pinto0528/alpa/Documentacion/Modelo_de_negocio/canales_relacion.md

# Canales y Relación con Clientes

## Canales de Distribución

El sistema se distribuye a través de tres canales principales, segmentados según el tipo de cliente:

| Canal | Segmento | Descripción |
|---|---|---|
| **Venta directa** | Productores agropecuarios | El equipo comercial contacta directamente al productor, realiza una visita al campo para relevar necesidades, propone una configuración de nodos y gateway, y gestiona la instalación. |
| **Alianzas con aseguradoras** | Aseguradoras agrícolas (B2B) | Las aseguradoras incluyen el sistema como beneficio o requisito en sus pólizas. La venta se canaliza a través de la aseguradora, que actúa como prescriptora y canal de distribución masivo. |
| **Cooperativas y asociaciones agrícolas** | Productores asociados | Las cooperativas difunden el sistema entre sus miembros, facilitan la compra grupal (descuentos por volumen) y centralizan la instalación en una zona geográfica, reduciendo costos logísticos. |

### Esquema de Distribución por Segmento

| Segmento | Canal Primario | Canal Secundario | Modelo de Venta |
|---|---|---|---|
| **Productor pequeño-mediano** | Cooperativa / asociación | Venta directa digital | Kit básico, pago financiado |
| **Productor mediano-grande** | Venta directa | Aseguradora (derivación) | Kit estándar, contado o suscripción anual |
| **Agroindustria / ingenio** | Venta directa corporativa | Aseguradora (co-branding) | Kit premium, suscripción corporativa |
| **Aseguradora** | Comercial B2B | — | Licencia anual por cliente asegurado |
| **Gobierno / municipio** | Licitación / convenio | — | Licencia institucional por territorio |

---

## Canales de Comunicación

| Canal | Propósito | Segmento |
|---|---|---|
| **Sitio web institucional** | Presentación del sistema, casos de uso, solicitud de contacto, tienda online | Todos los segmentos |
| **Demostraciones en campo** | Instalación piloto gratuita en campos de productores referentes. Validación en terreno con bomberos. | Productores, bomberos, HyS |
| **Referencias de productores** | Programa de embajadores: productores que ya usan el sistema recomiendan a pares. Efecto "boca a boca" en zonas rurales. | Productores |
| **Redes comerciales de aseguradoras** | Los ejecutivos de cuenta de las aseguradoras ofrecen el sistema a sus asegurados como servicio de prevención. | Productores (vía aseguradora) |
| **Charlas y capacitaciones** | Talleres en cooperativas, sociedades rurales y facultades. Demostración del impacto del sistema. | Productores, bomberos, estudiantes |
| **Atención telefónica / WhatsApp** | Soporte pre-venta y post-venta. Canal directo con el equipo emprendedor. | Todos los segmentos |

---

## Relación con Productores

### Antes de la Venta (Captación)

1. **Contacto inicial:** el productor llega por referencia, web, aseguradora o cooperativa
2. **Relevamiento del campo:** visita técnica para evaluar extensión, topografía, puntos críticos, conectividad disponible
3. **Propuesta personalizada:** configuración de nodos y gateway según las necesidades del establecimiento
4. **Demostración:** instalación de 1-2 nodos de prueba por 15 días para que el productor valide el funcionamiento

### Durante la Venta (Instalación)

| Actividad | Responsable | Duración Estimada |
|---|---|---|
| Instalación de nodos en campo | Técnico de campo | 1 día para predios de hasta 500 ha |
| Configuración de gateway y conectividad | Técnico de campo | 2-3 horas |
| Capacitación del productor y su personal | Técnico de campo | 2 horas |
| Activación de dashboard y alertas | Equipo de software | Inmediato |

### Post-Venta

| Actividad | Frecuencia | Canal |
|---|---|---|
| **Soporte técnico** | 24/7 para emergencias, horario laboral para consultas generales | WhatsApp / llamada / remoto |
| **Actualización de firmware** | Trimestral o ante nueva funcionalidad | OTA (over-the-air) vía gateway |
| **Mantenimiento preventivo** | Semestral (antes de temporada crítica) | Visita técnica |
| **Reporte de actividad** | Mensual vía email | Dashboard exportable |
| **Renovación de suscripción** | Anual | Automática / recordatorio |

---

## Relación con Aseguradoras

| Actividad | Frecuencia | Descripción |
|---|---|---|
| **Reportes periódicos de siniestralidad** | Trimestral | Dashboard con métricas de los asegurados que tienen el sistema instalado: alertas disparadas, tiempo de respuesta, siniestros evitados. |
| **Auditoría de datos** | Anual | Verificación independiente de la integridad de los registros del sistema. Cada evento tiene un hash que garantiza su inalterabilidad. |
| **Reuniones comerciales** | Bimestral | Revisión de métricas de adopción, ajuste de bonificaciones, planificación de nuevos despliegues. |
| **Co-branding** | Por campaña | Material de comunicación conjunto: la aseguradora comunica el beneficio a sus asegurados con la marca del sistema. |

### Modelo de Relación

> La aseguradora no es solo un cliente: es un **canal de distribución estratégico**. Su fuerza de ventas ya tiene relación con los productores. Cada ejecutivo de cuenta que recomienda el sistema es un vendedor en terreno sin costo fijo para el proyecto.

---

## Captación de Clientes por Etapa

| Etapa | Actividad | Métrica de Éxito |
|---|---|---|
| **Lanzamiento (Año 1)** | Demostraciones gratuitas en 10 campos de productores referentes en Tucumán. Charlas en 3 cooperativas agrícolas. Presentación en 2 ingenios azucareros. | 10 instalaciones piloto, 35 kits vendidos |
| **Crecimiento (Año 2)** | Programa de referidos con descuento. Alianza con 1 aseguradora. Presencia en 2 ferias agrícolas del NOA. | 85 kits vendidos, 30% por canal aseguradora |
| **Expansión (Año 3)** | Expansión a Córdoba y Litoral. 2 aseguradoras activas. Distribución en cooperativas de 4 provincias. | 190 kits vendidos, 50% por canal aseguradora |

---

## Matriz de Canales y Relación por Segmento

| Segmento | Canal de Distribución | Canal de Comunicación | Tipo de Relación | Intensidad |
|---|---|---|---|---|
| **Productor** | Venta directa / cooperativa / aseguradora | WhatsApp, demostraciones, referidos | Personalizada, soporte técnico continuo | Alta |
| **Aseguradora** | Comercial B2B | Reportes, reuniones, dashboard | Contractual, datos auditables | Alta |
| **Bomberos / brigadas** | Sin costo (beneficiario estratégico) | Coordinación directa | Colaboración, validación técnica | Media |
| **HyS industrial** | Venta directa corporativa | Demostraciones, capacitaciones | Técnica, cumplimiento normativo | Media |
| **Gobierno / municipio** | Licitación / convenio | Presentaciones institucionales | Contractual, monitoreo territorial | Baja (escalamiento futuro) |

---

*Documento perteneciente al proyecto Sistema de Alerta de Incendios Rurales*
