pinto0528/alpa/Documentacion/Modelo_de_negocio/propuesta_valor.md

# Propuesta de Valor

## Declaración de Propuesta de Valor

Un sistema autónomo de detección temprana de incendios que alerta al productor agropecuario en menos de 5 minutos —sin depender de señal celular, electricidad de red ni vigilancia humana— evitando pérdidas millonarias, protegiendo vidas y reduciendo el tiempo de respuesta de 40 minutos a minutos.

---

## Mapa de Valor por Segmento

### 1. Para Productores Agropecuarios

#### Beneficios

| Beneficio | Descripción | Impacto Cuantitativo |
|---|---|---|
| **Detección en menos de 5 minutos** | Sensores detectan humo, temperatura anormal o llama en etapa incipiente y disparan alerta inmediata | Reduce tiempo de detección de 30-40 min a <5 min |
| **Sin dependencia de conectividad** | Comunicación vía LoRa/LoRaWAN entre nodos y gateway. No requiere señal celular ni internet | Opera en el 100% del campo, incluso en zonas sin cobertura |
| **Autonomía energética total** | Paneles solares + baterías. No requiere conexión a red eléctrica | Funcionamiento continuo 24/7 durante toda la temporada crítica |
| **Alerta con geolocalización GPS** | Cada alerta incluye coordenadas exactas del nodo que detectó el evento | Permite ir directo al foco sin perder tiempo buscando |
| **Cobertura 24/7** | Monitoreo continuo, incluso de noche o en zonas alejadas | Donde hoy es imposible tener ojos, el sistema nunca se desconecta |
| **Reportes digitales para seguros** | Registro inalterable de activación, alertas y estado del sistema | Respaldos para reclamar bonificaciones de póliza o agilizar indemnizaciones |
| **Protección de activos críticos** | Cobertura específica para zonas de alto valor: sistemas de riego, galpones, cultivos intensivos | Un incendio detectado a tiempo puede salvar USD 80.000+ en infraestructura de riego |

#### Aliviadores de Dolores Específicos

| Dolor Actual | Cómo lo Alivia el Sistema |
|---|---|
| *"Nos enteramos siempre tarde"* | Alerta automática en <5 minutos desde que se inicia el foco |
| *"De noche es imposible tener ojos en todos lados"* | Sensores infrarrojos + detección de humo funcionan 24/7 |
| *"La señal de celular ahí adentro es nula"* | Comunicación LoRa sin necesidad de antena celular ni internet |
| *"Perdí 40 ha de limón y USD 80.000 en riego"* | Detección temprana permite actuar antes de que el fuego alcance zonas críticas |
| *"Te da una impotencia bárbara no poder hacer nada"* | Pasividad → Proactividad. El productor recibe la alerta y actúa en minutos |

#### Propuesta de Valor en una Frase

> "Sepa dónde y cuándo se inició un incendio en su campo, aunque no haya señal celular, antes de que sea demasiado tarde."

---

### 2. Para Aseguradoras Agrícolas

#### Beneficios

| Beneficio | Descripción | Impacto Cuantitativo |
|---|---|---|
| **Reducción de siniestralidad** | Los productores con sistema instalado detectan incendios en <5 min, reduciendo drásticamente la probabilidad de pérdida total | Potencial de reducir siniestros graves en un 60-80% (estimación propia basada en entrevistas con aseguradores, Tucumán, 2026) |
| **Reportes digitales auditables** | Cada nodo genera registros cifrados e inalterables de su estado y eventos detectados | Evidencia sólida para ajustar primas y validar cobertura |
| **Bonificaciones justificables** | Descuentos en pólizas vinculados a datos objetivos de prevención | Ventaja competitiva frente a otras aseguradoras |
| **Diferenciación de mercado** | Ofrecer un servicio de prevención tecnológica como valor agregado en la póliza | Atrae y retiene asegurados preocupados por incendios |
| **Reducción de falsos siniestros** | Los reportes del sistema permiten verificar si realmente hubo un evento de incendio | Menos litigios, menos fraudes |

#### Propuesta de Valor en una Frase

> "Convierta la prevención de incendios de sus asegurados de un deseo en un dato verificable, y ajuste sus primas con evidencia objetiva."

---

### 3. Para Bomberos Voluntarios y Brigadas Forestales

#### Beneficios

| Beneficio | Descripción | Impacto Cuantitativo |
|---|---|---|
| **Geolocalización precisa del foco** | Coordenadas GPS exactas del nodo que disparó la alerta | Elimina la búsqueda a ciegas. Llegan directo al punto |
| **Intervención en etapa incipiente** | Reciben alerta cuando el fuego aún es una chispa | Extinción con recursos ligeros: camioneta + 4 brigadistas + mochilas |
| **Información de acceso al campo** | Datos de tranqueras, caminos internos, puntos de agua cercanos | Reducción del tiempo de acceso y del riesgo operativo |
| **Reducción de riesgo para el personal** | No combaten llamas descontroladas de 5 metros | Menos exposición, menos accidentes |

> *"Si tu sistema nos manda las coordenadas GPS exactas al celular cuando recién es una chispa, nosotros mandamos rápido una camioneta liviana con cuatro chicos y mochilas de agua, y lo apagamos en diez minutos."*
> — Bombero voluntario, Tucumán

#### Propuesta de Valor en una Frase

> "Llegue al incendio cuando todavía es una chispa, con coordenadas exactas y sin poner en riesgo a su brigada."

---

### 4. Para Responsables de Higiene y Seguridad Industrial

#### Beneficios

| Beneficio | Descripción | Impacto Cuantitativo |
|---|---|---|
| **Activación inmediata de evacuación** | Alerta directa a panel de control sin cadena de aviso | Reduce tiempo de activación de evacuación de >10 min a <1 min |
| **Geolocalización para zonificar riesgo** | Saber exactamente dónde está el foco permite evacuar solo los sectores necesarios | Evita paralizaciones innecesarias de planta |
| **Cumplimiento normativo documentado** | Registro automático de todas las alertas, tiempos de respuesta y acciones tomadas | Respaldo ante SRT, aseguradoras, autoridades ambientales |
| **Protección de la vida de operarios** | Maquinistas, tractores y personal de campo reciben alerta temprana | Diferencia entre evacuación segura y tragedia |

#### Propuesta de Valor en una Frase

> "Active protocolos de evacuación en segundos, no en minutos, y proteja la vida de su personal con datos auditables."

---

## Diferenciación Frente a Alternativas Actuales

| Dimensión | Vigilancia Visual | Satélites (NASA, GMIS) | Faros de Conservación | Pampa 4 / Telecom Agro IoT | **Nuestro Sistema** |
|---|---|---|---|---|---|
| **Detección automática** | No | Sí (focos de calor) | Sí (cámaras) | Sí (sensores IoT) | **Sí — sensores multi-parámetro** |
| **Etapa de detección** | Cuando hay humo visible | Fuego ya desarrollado | Fuego ya desarrollado | Depende del sensor | **Etapa incipiente** |
| **Funciona sin conectividad** | Sí (depende de persona) | No (requiere internet) | No (requiere red) | No (requiere red) | **Nodo→Gateway: Sí (LoRa) / Gateway→Nube: WiFi o 4G** |
| **Autonomía energética** | N/A | N/A | No (requiere red) | Limitada | **Sí — panel solar + batería** |
| **Alerta directa al productor** | No | No (organismos) | No (central de monitoreo) | Sí (app/web) | **Sí — SMS/radio/LoRa** |
| **Cobertura 24/7** | No (solo de día) | Sí (pasada satelital) | Sí | Sí | **Sí** |
| **Costo para el productor** | Alto (personal dedicado) | Gratuito (público) | Muy alto (gobiernos) | Alto (suscripción + datos) | **Accesible (kit + suscripción básica)** |
| **Geolocalización GPS** | No | Aproximada (1 km+) | Sí (cámaras) | Sí | **Sí (precisa por nodo)** |
| **Reportes digitales auditables** | No | No | No | Limitado | **Sí — blockchain/hash de eventos** |

---

## Matriz de Valor: Nivel de Impacto por Segmento

| Beneficio | Productor | Aseguradora | Bomberos | HyS (Hig. y Seg.) | Gobierno |
| :--- | :---: | :---: | :---: | :---: | :---: |
| **Detección en <5 min** | Crítico | Crítico | Crítico | Crítico | Alto |
| **Sin conectividad (Offline)** | Crítico | Alto | Alto | Alto | Medio |
| **Autonomía energética** | Crítico | Bajo | Bajo | Alto | Alto |
| **Geolocalización GPS** | Crítico | Bajo | Crítico | Crítico | Alto |
| **Cobertura 24/7** | Crítico | Alto | Alto | Crítico | Alto |
| **Reportes auditables** | Alto | Crítico | Bajo | Crítico | Alto |
| **Activación de evacuación** | Alto | Bajo | Bajo | Crítico | Bajo |
| **Reducción de siniestralidad** | Crítico | Crítico | Bajo | Alto | Alto |

---

*Documento perteneciente al proyecto Sistema de Alerta de Incendios Rurales*
*Fuentes: entrevistas a productores, bomberos, aseguradores y responsables de HyS (Tucumán, 2026); sitio web Pampa 4 (pampa4.ar); Valor Agregado Agro (2025); InfoMerlo (2026); La Estafeta (2026); NASA ARSET / FIRMS*
