pinto0528/alpa/Documentacion/Modelo_de_negocio/proposito.md

# Propósito

## Razón de Ser

**Que ningún productor agropecuario pierda su campo, su sustento o su patrimonio por no tener acceso a tecnología de detección temprana de incendios.**

## Declaración de Propósito

N.T. nace para cerrar la brecha tecnológica que hoy deja indefensos a los productores rurales argentinos. Mientras los incendios arrasan miles de hectáreas cada año, las soluciones existentes están diseñadas para gobiernos o grandes corporaciones, no para el productor individual que trabaja en un campo sin señal celular ni electricidad de red.

## Motivación

El proyecto surge de la realidad tucumana: en la zafra 2025 se quemaron más de 55.000 hectáreas de caña de azúcar, citrus y bosques nativos. Productores que invirtieron toda su vida en el campo vieron cómo el fuego lo consumía todo antes de que pudieran enterarse. El equipo N.T., integrado por estudiantes de la UTN Facultad Regional Tucumán, decidió que eso no debía seguir pasando.

## Cambio que Buscamos Generar

- **De reactivo a preventivo:** que el productor sepa del incendio cuando todavía es una chispa, no cuando ya es un infierno
- **De excluyente a accesible:** tecnología de detección temprana al alcance del productor mediano, no solo de grandes agroindustrias o gobiernos
- **De individual a comunitario:** un sistema que también protege a vecinos, brigadas y comunidades enteras

---

*Documento perteneciente al proyecto Sistema de Alerta de Incendios Rurales*
