pinto0528/alpa/Documentacion/Problema_y_contexto/causas_consecuencias.md

# Causas y Consecuencias de los Incendios Rurales en Argentina

## Causas

### Causas Raíz

| Causa | Descripción | Evidencia/Fuente |
|---|---|---|
| **Falta de monitoreo en tiempo real** | Las zonas rurales aisladas no cuentan con ningún sistema de vigilancia que detecte focos ígneos en etapa incipiente | Los sistemas satelitales gubernamentales reportan cuando el fuego ya tiene magnitud (Río Negro SPLIF, 2026) |
| **Escasa o nula conectividad** | Gran parte del territorio rural argentino no tiene cobertura de red celular ni internet, imposibilitando la comunicación de alertas | Telecom Agro IoT: "aún falta conectar muchas zonas rurales" (Agroleaks, 2025) |
| **Quema ilegal de pastizales y rastrojos** | Práctica extendida e ilegal que frecuentemente se sale de control, especialmente con condiciones de viento y sequía | Ley 6.253 Tucumán: prohibición de quema; multas y denuncias penales (Comunicación Tucumán, 2025) |
| **Condiciones climáticas extremas** | Sequías prolongadas, heladas severas y fuertes vientos crean biomasa altamente combustible | Tucumán 2024: heladas de -5,8°C durante 40+ horas aumentaron combustibilidad (EEAOC, 2024) |

### Causas Contribuyentes

| Causa | Descripción | Evidencia/Fuente |
|---|---|---|
| **Acumulación de biomasa seca** | Pastos, rastrojos y vegetación seca que actúan como combustible | INTA recomienda ajuste de carga ganadera y pastoreo rotativo (Infocampo, 2025) |
| **Maquinaria agrícola sin mantenimiento** | Motores sobrecalentados, pérdidas de combustible y chispas generan focos de incendio | Guía de buenas prácticas: controlar estado de maquinaria (Min. Bioagroindustria Córdoba, 2025) |
| **Descuido humano** | Colillas de cigarrillos, quema de basura, fogones mal apagados | INTA: "incendios con origen en causas evitables" (INTA, 2025) |
| **Falta de cortafuegos y picadas** | Propiedades sin fajas cortafuego perimetrales ni internas | Ley 10.958/24 Córdoba: obligación de mantener picadas y fajas cortafuego |
| **Rayos y fenómenos naturales** | Descargas eléctricas durante tormentas secas | INTA: "pueden deberse a fenómenos naturales como rayos" (INTA, 2025) |

## Consecuencias

### Consecuencias Directas

| Consecuencia | Descripción | Evidencia/Fuente |
|---|---|---|
| **Pérdida de cultivos y pasturas** | Destrucción total o parcial de la producción agrícola y ganadera | Tucumán 2025: 49.100 ha de caña quemadas (EEAOC) |
| **Muerte de animales** | Pérdida de ganado vacuno, ovino, porcino y fauna silvestre | INTA: "pérdidas económicas por destrucción de instalaciones, forrajes y animales" |
| **Destrucción de infraestructura** | Alambrados, galpones, silos, viviendas rurales, maquinaria | INTA: impacto en instalaciones y equipos |
| **Pérdidas económicas devastadoras** | Desde USD 310.000 hasta más de USD 11 millones por establecimiento | INTA/FAO: análisis económico de pérdidas (2025) |
| **Pérdida de vidas humanas** | Riesgo directo para familias rurales, bomberos y brigadistas | CPIA: "los incendios no son desastres inevitables" (2026) |

### Consecuencias Indirectas

| Consecuencia | Descripción | Evidencia/Fuente |
|---|---|---|
| **Degradación de suelos** | Pérdida de materia orgánica, erosión, compactación | CPIA: impacto ambiental y degradación de ecosistemas |
| **Pérdida de biodiversidad** | Destrucción de hábitats de fauna nativa y flora autóctona | Córdoba 2024: 29.965 ha de áreas protegidas afectadas (IDECOR) |
| **Contaminación del aire** | Emisiones de CO2, material particulado y gases tóxicos | CPIA: "emisiones de gases" como consecuencia de incendios |
| **Impacto en cuencas hídricas** | Alteración del ciclo del agua, sedimentación, contaminación | Córdoba: sierras son cabecera de 5 cuencas hídricas (TN, 2025) |
| **Accidentes viales** | Humo en rutas y autopistas que reduce visibilidad | Comunicación Tucumán: "accidentes viales en las rutas tucumanas" (2025) |
| **Interrupción de servicios eléctricos** | Incendios cerca de tendidos eléctricos provocan desenganches | Comunicación Tucumán: "desenganche de sistemas eléctricos" (2025) |
| **Impacto en la seguridad alimentaria** | Reducción de la producción agropecuaria regional | CPIA: "seguridad alimentaria, sostenibilidad de ecosistemas" (2026) |
| **Estrés psicológico y social** | Ansiedad, incertidumbre y deterioro de la calidad de vida rural | INTA: "efectos sociales por riesgo a personas y deterioro de calidad de vida" |

## Ciclo del Problema

```
Falta de detección temprana
        │
        ▼
Foco ígneo no detectado en etapa incipiente
        │
        ▼
Propagación rápida (viento + biomasa seca)
        │
        ▼
Detección tardía (visual o satelital)
        │
        ▼
Respuesta insuficiente o tardía
        │
        ▼
Incendio de gran magnitud
        │
        ▼
Pérdidas económicas, ambientales y humanas
        │
        ▼
Sin aprendizaje sistémico → Se repite el ciclo
```

---

*Documento perteneciente al proyecto Sistema de Alerta de Incendios Rurales*
*Fuentes: CPIA, INTA, IDECOR, EEAOC, La Gaceta, Revista Chacra, Comunicación Tucumán, TN, Infocampo, Agroleaks*
