pinto0528/alpa/Documentacion/Problema_y_contexto/descripcion_problema.md

# Descripción del Problema

## Enunciado

Los productores agropecuarios argentinos que operan en zonas rurales con escasa o nula infraestructura de conectividad carecen de sistemas accesibles de detección temprana de incendios. Como consecuencia, los focos ígneos se descubren cuando ya han alcanzado una magnitud significativa, imposibilitando una respuesta efectiva y generando pérdidas económicas, ambientales y sociales devastadoras.

## Contexto

Argentina registra de manera sostenida más de **10.000 incendios rurales por año** (CPIA, 2026). Esta problemática afecta a todo el territorio nacional, con episodios particularmente severos en provincias como Córdoba, Corrientes, La Pampa, Chubut, y la región del NOA (Tucumán, Salta, Jujuy, Catamarca).

El problema se manifiesta con mayor intensidad durante la **temporada seca** (julio a octubre en la mayor parte del país), cuando las condiciones de baja humedad, fuertes vientos y acumulación de biomasa vegetal seca crean el escenario ideal para la propagación rápida del fuego.

En Tucumán, provincia desde donde se desarrolla este proyecto, la situación es crítica: durante la zafra 2025 se quemaron **49.100 hectáreas de caña de azúcar** más **6.770 hectáreas** de otros cultivos, áreas deforestadas y bosques nativos (EEAOC, 2025).

## ¿Por qué es un problema real?

### Evidencia cuantitativa

| Indicador | Valor | Fuente |
|---|---|---|
| Incendios anuales en Argentina | +10.000 | CPIA |
| Hectáreas afectadas (2020) | 1.150.000 | CPIA |
| Hectáreas afectadas (2021-2022) | 1.054.000 | CPIA |
| Hectáreas quemadas en Córdoba (2024) | 103.327 | IDECOR |
| Hectáreas quemadas en Tucumán (2025) | 55.870 | EEAOC / La Gaceta |
| Pérdidas en campo de 650 ha (30% afectación) | USD 310.277 | INTA/FAO |
| Pérdidas en campo de 10.000 ha (100% afectación) | USD 11.160.675 | INTA/FAO |

### Evidencia cualitativa

- El enfoque actual es **reactivo**: se actúa cuando el incendio ya está declarado (CPIA, 2026)
- Los sistemas de alerta satelital gubernamentales detectan el fuego cuando **ya tiene magnitud**, no en etapa incipiente
- Los productores en zonas sin cobertura de red no reciben alertas de ningún tipo
- Las soluciones tecnológicas existentes (Pampa 4, Faros de Conservación) están orientadas a gobiernos o grandes empresas, no al productor individual

## El problema en una frase

> Un productor agropecuario en una zona rural sin infraestructura puede perder todo su campo, su sustento y su patrimonio antes de siquiera enterarse de que hay un incendio.

---

*Documento perteneciente al proyecto Sistema de Alerta de Incendios Rurales*
*Fuentes: CPIA, INTA, IDECOR, EEAOC, La Gaceta, Revista Chacra, Argentina.gob.ar*
