pinto0528/alpa/Documentacion/Problema_y_contexto/impacto_productores.md

# Nivel de Dolor de los Afectados

## Perfil del Afectado

**Productor agropecuario o dueño de campo** en zonas rurales con escasa o nula infraestructura de conectividad y servicios.

---

## Intensidad del Impacto

### Económico

El impacto económico de un incendio rural es **devastador** y puede significar la pérdida total del sustento:

| Escala | Consecuencia Económica |
|---|---|
| **Pequeño productor (< 500 ha)** | Un incendio puede significar la pérdida de su único ingreso anual. No tiene capacidad de absorber el impacto. |
| **Mediano productor (500 - 5.000 ha)** | Pérdidas que van desde USD 310.000 hasta más de USD 1.000.000. Puede requerir endeudamiento para recuperarse. |
| **Gran productor (> 5.000 ha)** | Pérdidas que superan los USD 3.000.000 - USD 11.000.000. Impacto significativo aunque tenga mayor resiliencia financiera. |

### Productivo

- **Pérdida de cultivos en pie:** meses o años de trabajo destruidos en horas
- **Muerte de ganado:** animales que no pueden escapar del fuego
- **Destrucción de infraestructura:** alambrados, galpones, silos, viviendas, maquinaria
- **Degradación del suelo:** el suelo quemado pierde fertilidad y capacidad productiva por años

### Emocional y Social

- **Estrés y ansiedad permanente** durante la temporada de riesgo
- **Sensación de impotencia:** no poder hacer nada si no se detecta a tiempo
- **Impacto en la familia:** riesgo de vidas propias y de la comunidad
- **Aislamiento:** en zonas remotas, la ayuda tarda en llegar

---

## Frecuencia del Problema

### Estacionalidad

El problema no es constante durante todo el año, pero cuando se manifiesta lo hace con una **recurrencia predecible**:

| Región | Temporada Crítica | Duración |
|---|---|---|
| Córdoba | Julio - Octubre | ~4 meses |
| Tucumán / NOA | Junio - Octubre | ~5 meses |
| Patagonia | Diciembre - Marzo | ~4 meses |
| Litoral | Agosto - Noviembre | ~4 meses |

### Recurrencia Anual

- **Más de 10.000 incendios por año** a nivel nacional (CPIA)
- En Tucumán, **todos los años** se queman entre 49.000 y 67.000 hectáreas de caña
- En Córdoba, **todos los años** se registran entre 500 y 700 incendios
- Un productor puede enfrentar **múltiples episodios** en una sola temporada

---

## Urgencia

### ¿Por qué necesitan resolverlo AHORA?

1. **El fuego no espera:** un foco ígneo puede pasar de ser controlable a incontrolable en **minutos** con las condiciones adecuadas (viento, sequía, biomasa)

2. **La detección tardía es la diferencia entre un problema menor y una catástrofe:**
   - Detectado en los primeros 15 minutos: extinción con recursos básicos
   - Detectado después de 1 hora: requiere brigadas y equipamiento
   - Detectado después de 3 horas: incendio incontrolable, pérdidas totales

3. **La temporada de riesgo está siempre a la vuelta de la esquina:** para un productor en el NOA, la próxima temporada seca comienza en **junio**

4. **No hay alternativa efectiva hoy:** las soluciones existentes no llegan al productor individual en zonas sin infraestructura

---

## Soluciones Actuales: Cómo Enfrentan el Problema Hoy

### Lo que hacen los productores actualmente

| Acción | Descripción | Limitaciones |
|---|---|---|
| **Vigilancia visual** | El productor o sus empleados miran el horizonte buscando humo | Solo funciona de día, con buena visibilidad, y cuando alguien está mirando. No hay vigilancia 24/7 |
| **Llamar a bomberos** | Cuando detectan humo, llaman al cuartel de bomberos voluntarios más cercano | Para cuando llaman, el fuego ya tiene magnitud. En zonas remotas, los bomberos tardan horas en llegar |
| **Cortafuegos manuales** | Crean fajas cortafuego perimetrales como prevención | Requiere mantenimiento constante. No detecta, solo contiene |
| **Seguros agropecuarios** | Contratan seguros que cubren pérdidas por incendio | No previenen el incendio. Solo compensan económicamente después del daño. No todos tienen acceso |
| **Certificaciones "sin fuego"** | Programas voluntarios como "Caña de azúcar sin uso del fuego" | Reducen riesgo pero no eliminan la posibilidad de incendios por causas externas |
| **Sistemas satelitales gubernamentales** | Alertas de focos de calor por satélite (NASA, etc.) | Detectan cuando el fuego ya tiene magnitud (no en etapa incipiente). No llegan al productor individual en zonas sin conectividad |

### Gaps no cubiertos

| Necesidad | Gap |
|---|-----|
| **Detección en etapa incipiente** | Ninguna solución accesible detecta el fuego cuando aún es controlable |
| **Autonomía en zonas sin infraestructura** | Las soluciones existentes requieren conectividad, electricidad de red o infraestructura que no existe |
| **Alerta directa al productor** | Los sistemas gubernamentales alertan a organismos, no al dueño del campo |
| **Accesibilidad económica** | Soluciones como Pampa 4 o Faros de Conservación están fuera del alcance del productor individual |
| **Monitoreo 24/7** | La vigilancia visual humana no puede operar de noche ni de forma continua |
| **Escalabilidad** | No hay solución que un productor pueda instalar en su campo de forma independiente |

---

## Resumen del Nivel de Dolor

| Dimensión | Nivel | Justificación |
|---|---|---|
| **Intensidad** | **Muy Alto** | Pérdidas de USD 310K a USD 11M por evento. Puede significar la quiebra del productor |
| **Frecuencia** | **Alta (estacional)** | Cada año, durante 4-5 meses de temporada crítica |
| **Urgencia** | **Crítica** | La diferencia entre detección temprana y tardía es de minutos. No se puede postergar |

---

*Documento perteneciente al proyecto Sistema de Alerta de Incendios Rurales*
*Fuentes: CPIA, INTA, IDECOR, EEAOC, La Gaceta, Revista Chacra, Infocampo, Comunicación Tucumán*
