pinto0528/alpa/Documentacion/Validacion/dolores_frustraciones.md

# Dolores y Frustraciones

## Dolores Emocionales

| Dolor | Descripción | Testimonio |
|---|---|---|
| **Impotencia** | Sensación devastadora de enterarse tarde de un incendio, cuando el fuego ya está fuera de control y las posibilidades de detenerlo son mínimas | *"Te da una impotencia bárbara"* — Productor agrícola |
| **Miedo a perderlo todo** | Temor constante a perder cultivos completos, especialmente en producciones de alto valor como el limón, donde un incendio destruye no solo la plantación sino también sistemas de riego extremadamente costosos | *"Mi verdadero terror es el limón: un fuego que cruza del cañaveral a la quinta me derrite kilómetros de mangueras de riego por goteo. Reponer eso hoy, con los precios en dólares, te quiebra"* — Productor en Tafí Viejo |
| **Estrés permanente** | Preocupación por la seguridad de trabajadores, maquinistas y brigadistas. Muchos productores viven en estado de alerta constante durante toda la temporada crítica (agosto-septiembre) | *"En agosto y septiembre ponemos a los muchachos a dar vueltas en moto, pero de noche o en los fondos de la finca es imposible tener ojos en todos lados"* — Productor agrícola |
| **Sensación de desamparo** | Saber que no hay un sistema que los alerte a tiempo y que dependen de la suerte o de que un vecino vea humo | *"La señal de celular ahí adentro es nula, así que un equipo que mande alertas solo sería un golazo"* — Productor agrícola |

## Dolores Prácticos

| Dolor | Descripción | Impacto |
|---|---|---|
| **Pérdidas económicas millonarias** | Daños en cultivos, maquinaria agrícola, infraestructura y sistemas de riego por goteo | Desde USD 310.000 hasta más de USD 11 millones por establecimiento (INTA/FAO) |
| **Tiempo de respuesta demasiado lento** | Dependen de vigilancia humana o de que un vecino detecte humo a la distancia. Cuando inician la intervención, el fuego ya avanzó considerablemente | 30-40 minutos desde que se detecta hasta que se logra armar un cortafuego |
| **Mala conectividad** | No existe señal celular estable en zonas rurales para comunicar rápidamente la emergencia. Dificulta la coordinación interna y el aviso a bomberos | Imposibilidad de usar soluciones basadas en celular o internet |
| **Retrasos en la zafra** | Paralización de actividades productivas y altos costos operativos para combatir incendios ya desarrollados | Impacto directo en la producción y los ingresos |
| **Costos de combate** | Combustible, agua, desgaste de maquinaria y horas de trabajo para intentar contener incendios que ya son incontrolables | Miles de litros de agua y combustible desperdiciados |

## Dolores Sociales

| Dolor | Descripción | Impacto |
|---|---|---|
| **Contaminación ambiental** | Humo y cenizas que generan problemas respiratorios en la población de comunidades cercanas | "Lluvia negra" (cenizas) que afecta barrios linderos |
| **Riesgo de vidas humanas** | Peligro constante para trabajadores rurales y bomberos voluntarios que intervienen sin información precisa sobre el foco del incendio | *"Terminamos arriesgando la vida de nuestro personal, combatiendo llamas gigantes por horas"* — Bombero voluntario |
| **Conflictos legales y sanciones** | Productores que enfrentan multas por normativas ambientales (Ley 6.253 Tucumán) y de seguridad laboral (SRT) cuando los incendios provocan daños mayores | Multas ambientales y denuncias penales |
| **Pérdida de fuentes de trabajo** | Cuando las producciones se ven afectadas, los trabajadores agrícolas pierden su empleo | Impacto en la economía de comunidades rurales enteras |

---

## Resumen del Dolor

> *"Si yo tuviera un detector que me dé 5 minutos de ventaja ni bien arranca el foco, puedo activar los protocolos de evacuación al instante. Esos minutos valen oro."*
> — Responsable de Higiene y Seguridad, ingenio azucarero

El dolor del productor agropecuario frente a los incendios rurales es **multidimensional**: económico (pérdidas millonarias), emocional (impotencia, miedo, estrés), social (riesgo de vidas, contaminación) y operativo (falta de herramientas efectivas). La necesidad de detección temprana no es un lujo: es una cuestión de supervivencia.

---

*Documento perteneciente al proyecto Sistema de Alerta de Incendios Rurales*
*Fuentes: Entrevistas realizadas a productores, bomberos, aseguradores y responsables de seguridad (Tucumán, 2026)*
