pinto0528/alpa/Documentacion/Validacion/entrevistas.md

# Entrevistas de Validación

## Metodología

Se realizaron entrevistas semi-estructuradas a los principales stakeholders afectados por la problemática de incendios rurales en Tucumán y el NOA. El objetivo fue comprender en profundidad sus dolores, comportamientos actuales y necesidades no cubiertas.

---

## 1. Productor Agrícola

**Perfil:** Finca mixta de caña de azúcar y limón en Tafí Viejo / Lules, Tucumán
**Tamaño:** ~800 hectáreas (600 ha caña + 200 ha limón)

### Pregunta clave
¿Cómo manejan hoy el aviso de un incendio, qué tiempos de respuesta tienen y qué es lo que más les duele perder económicamente?

### Respuesta

> "Mirá, nos enteramos siempre tarde. O te avisa un vecino que pasó por la ruta 301 y vio la columna de humo, o nos damos cuenta cuando ya tenemos el fuego encima. Fácil pasan 30 o 40 minutos hasta que logramos enganchar la rastra al tractor para hacer un cortafuego. Te da una impotencia bárbara.
>
> Lo que la gente de la ciudad a veces no entiende es que en la caña perdemos el rastrojo, que es vital para guardar la humedad en el suelo ahora que las sequías vienen tan duras. Pero mi verdadero terror es el limón: un fuego que cruza del cañaveral a la quinta me derrite kilómetros de mangueras de riego por goteo. Reponer eso hoy, con los precios en dólares, te quiebra.
>
> En agosto y septiembre ponemos a los muchachos a dar vueltas en moto, pero de noche o en los fondos de la finca es imposible tener ojos en todos lados. La señal de celular ahí adentro es nula, así que un equipo que mande alertas solo sería un golazo."

### Insights clave
- **Tiempo de respuesta actual:** 30-40 minutos desde detección hasta acción
- **Mayor pérdida económica:** sistemas de riego por goteo (USD 80.000+ por evento)
- **Pérdida invisible:** rastrojo de caña (esencial para retención de humedad en sequía)
- **Necesidad explícita:** alertas automáticas sin dependencia de conectividad celular

---

## 2. Responsable de Higiene y Seguridad

**Perfil:** Ingenio azucarero / Gran agroindustria en Tucumán
**Responsabilidad:** Seguridad de operarios, maquinistas y personal de campo

### Pregunta clave
¿Cómo impactan estos siniestros no planificados en la logística de la zafra y, sobre todo, en los protocolos de protección de su personal?

### Respuesta

> "Para nosotros, un fuego descontrolado no es solo un problema de Medio Ambiente que nos puede clavar una multa por la Ley 6.253, es un riesgo crítico para la vida de la gente. La zafra no frena, tenemos máquinas cosechadoras y tractores trabajando a mil por hora.
>
> Nuestro mayor miedo es que el fuego, con los vientos de agosto, arrincone a un maquinista. Si yo tuviera un detector que me dé 5 minutos de ventaja ni bien arranca el foco, puedo activar los protocolos de evacuación al instante. Esos minutos valen oro para cumplir con las normativas de la Superintendencia de Riesgos del Trabajo (SRT) y asegurar que todos salgan ilesos.
>
> Hoy dependemos de que el operario vea el humo, llame por radio a la base, la base me avise a mí... es una cadena lentísima. Si la alerta me llegara directo a un panel con la ubicación exacta, nos ahorraríamos desgracias y paralizaciones de planta."

### Insights clave
- **Riesgo principal:** vida de maquinistas atrapados por el fuego
- **Valor de 5 minutos:** diferencia entre evacuación segura y tragedia
- **Cadena de aviso actual:** operario → radio → base → responsable (demasiados eslabones)
- **Necesidad explícita:** alerta directa a panel con ubicación exacta
- **Cumplimiento normativo:** SRT, Ley 6.253 (multas ambientales)

---

## 3. Ejecutivo de Compañía de Seguros Agrícolas

**Perfil:** Sucursal San Miguel de Tucumán
**Especialidad:** Pólizas agropecuarias

### Pregunta clave
¿Qué condiciones exigen hoy para asegurar un campo y qué tan viable sería ofrecerle una bonificación al productor que instale este sistema de detección?

### Respuesta

> "En el NOA, y sobre todo en Tucumán durante la primavera, los sinisestros se nos va por las nubes. Las sequías que tuvimos, como las del 2022 y 2023, nos hicieron pagar pólizas millonarias por lotes enteros quemados.
>
> Hoy al productor le exigimos que tenga las calles cortafuegos limpias y personal de guardia, pero a veces no alcanza. Desde el punto de vista comercial, tu proyecto es súper viable. Si un cliente me demuestra que con tu sensor bajó su tiempo de respuesta de una hora a diez minutos, su riesgo de pérdida total se desploma. Yo le puedo justificar a la casa central una baja en el costo de su póliza sin problema.
>
> Eso sí: el dispositivo me tiene que generar algo que a mí me certifique que el equipo estaba encendido y monitoreando cuando arrancó el siniestro."

### Insights clave
- **Siniestralidad:** muy alta en Tucumán durante primavera
- **Condiciones actuales:** cortafuegos limpios + personal de guardia (insuficiente)
- **Viabilidad comercial:** alta - bonificación de póliza justificable
- **Requisito clave:** reporte digital inalterable como evidencia
- **Oportunidad de negocio:** alianza con aseguradoras como canal de venta

---

## 4. Bombero Voluntario

**Perfil:** Cuartel en zona de interfase - Yerba Buena / San Javier, Tucumán
**Experiencia:** Incendios en Cerro San Javier, Horco Molle

### Pregunta clave
¿Cuál es el mayor obstáculo logístico que enfrentan al recibir un aviso y cómo les cambiaría el panorama recibir datos exactos de manera temprana?

### Respuesta

> "Acordate de lo que fueron los incendios en el Cerro San Javier o en Horco Molle... llegamos siempre a ciegas. La gente llama desesperada cuando el fuego ya tiene cinco metros de alto y está saltando la ruta.
>
> El mayor problema es entrar al campo: nos metemos por caminos de tierra y terminamos topándonos con tranqueras cerradas con candado. Perdemos tiempo valioso buscando por dónde pasar el autobomba.
>
> Si tu sistema nos manda las coordenadas GPS exactas al celular cuando recién es una chispa, nosotros mandamos rápido una camioneta liviana con cuatro chicos y mochilas de agua, y lo apagamos en diez minutos. Hoy terminamos arriesgando la vida de nuestro personal, combatiendo llamas gigantes por horas, y gastando miles de litros de agua y combustible que nos cuesta muchísimo conseguir."

### Insights clave
- **Mayor obstáculo:** llegar sin información precisa (tranqueras cerradas, caminos desconocidos)
- **Tiempo actual de aviso:** cuando el fuego ya tiene 5 metros de alto
- **Escenario ideal:** alerta con GPS cuando "recién es una chispa"
- **Respuesta posible con alerta temprana:** camioneta liviana + 4 brigadistas + mochilas = extinción en 10 minutos
- **Costo actual:** riesgo de vidas, miles de litros de agua y combustible desperdiciados

---

## Resumen de Insights

| Stakeholder | Dolor Principal | Necesidad Clave | Valor Percibido |
|---|---|---|---|
| **Productor** | Se entera tarde, pierde cultivos y riego | Alertas automáticas sin celular | Salvar su patrimonio |
| **Higiene y Seguridad** | Riesgo de vida de operarios | 5 minutos de ventaja para evacuar | Cumplir SRT, evitar tragedias |
| **Seguros** | Pólizas millonarias por siniestros | Reporte digital inalterable | Reducir siniestralidad, bonificar pólizas |
| **Bomberos** | Llegan a ciegas, sin acceso | GPS exacto cuando es una chispa | Extinguir en 10 minutos, no en horas |

---

*Documento perteneciente al proyecto Sistema de Alerta de Incendios Rurales*
*Entrevistas realizadas en Tucumán, 2026*
