pinto0528/alpa/Documentacion/Validacion/perfil_usuario.md

# Perfil del Usuario

## Datos del Usuario Principal

| Dimensión | Descripción |
|---|---|
| **Datos demográficos** | Hombres y mujeres de 30 a 65 años. Residen en zonas rurales o periurbanas de Tucumán y otras provincias del NOA. En muchos casos son propietarios de fincas familiares o administradores de establecimientos agrícolas y agroindustriales. |
| **Datos socioeconómicos** | Productores medianos o grandes, empresas agroindustriales y propietarios rurales cuyos ingresos dependen directamente del rendimiento de las cosechas y la continuidad de la producción. Manejan inversiones importantes en maquinaria, sistemas de riego e infraestructura agrícola. |
| **Personalidad** | Personas trabajadoras, prácticas y orientadas a la prevención. Valoran la seguridad de sus trabajadores y la protección de sus cultivos. Tienen una fuerte cultura del esfuerzo y se apoyan en la experiencia y el conocimiento del campo. Son desconfiados de soluciones tecnológicas complejas pero abiertos a herramientas simples que resuelvan problemas concretos. |
| **Actitudes frente al problema** | Consideran los incendios rurales como una amenaza constante y crítica, especialmente durante la sequía y la zafra. Existe una sensación generalizada de preocupación e impotencia porque los incendios se detectan demasiado tarde. Perciben la necesidad de una solución tecnológica pero desconfían de sistemas que requieran conectividad que no tienen. |
| **Comportamientos** | Implementan vigilancia manual mediante recorridos en motos o camionetas. Utilizan radios de comunicación para coordinar. Mantienen personal de guardia durante la temporada crítica. Construyen y mantienen cortafuegos perimetrales. Dependen de avisos de vecinos y trabajadores para detectar incendios. |

---

## Persona Representativa

**Nombre:** Carlos, 52 años
**Ubicación:** Finca de 800 ha en Simoca, Tucumán
**Actividad:** Caña de azúcar (600 ha) + Limón (200 ha)
**Situación:** Cada agosto-septiembre vive en estado de alerta permanente. Pone a 2-3 empleados a recorrer el campo en moto, pero sabe que es insuficiente. Perdió 40 ha de limón en 2023 por un incendio que se originó en un cañaveral vecino. Cuando se enteró, el fuego ya había derretido 3 km de mangueras de riego por goteo. La reposición le costó más de USD 80.000.

---

## Fuentes de Información

| Fuente | Descripción |
|---|---|
| **Entrevistas a productores** | Productores agrícolas de Tucumán (caña de azúcar, limón) |
| **Entrevistas a responsables de seguridad** | Responsables de higiene y seguridad de ingenios azucareros |
| **Entrevistas a aseguradores** | Ejecutivos de compañías de seguros agrícolas en Tucumán |
| **Entrevistas a bomberos** | Bomberos voluntarios de cuarteles en zona de interfase |
| **Informes y reportes** | Información periodística y reportes sobre incendios rurales y sequías en Tucumán y el NOA |
| **Observación directa** | Prácticas actuales de monitoreo y prevención en establecimientos rurales |

---

*Documento perteneciente al proyecto Sistema de Alerta de Incendios Rurales*
*Fuentes: Entrevistas realizadas a productores, bomberos, aseguradores y responsables de seguridad (Tucumán, 2026)*
