pinto0528/alpa/Documentacion/Validacion/segmentos_afectados.md

# Segmentos Afectados por la Problemática

## Segmento Principal

**Productores agropecuarios, dueños de fincas y empresas agroindustriales** de Tucumán y la región del NOA que operan en zonas rurales con escasa o nula infraestructura de conectividad.

### Características del segmento

- Trabajan principalmente en **cultivos extensivos**: caña de azúcar, limón, y otras producciones agrícolas
- Operan en zonas rurales con **alta exposición a incendios** durante épocas de sequía y zafra (agosto-septiembre)
- Gestionan **grandes extensiones territoriales** difíciles de monitorear de forma constante
- Muchos campos se encuentran en sectores donde la **señal celular es limitada o inexistente**

### Preocupación principal

Detectar el incendio en sus primeras etapas para:
- Reducir daños en cultivos, infraestructura, maquinaria y sistemas de riego
- Proteger la integridad física de sus trabajadores
- Evitar pérdidas económicas que pueden significar la quiebra del productor

> *"Mirá, nos enteramos siempre tarde. O te avisa un vecino que pasó por la ruta y vio la columna de humo, o nos damos cuenta cuando ya tenemos el fuego encima. Fácil pasan 30 o 40 minutos hasta que logramos enganchar la rastra al tractor para hacer un cortafuego. Te da una impotencia bárbara."*
> — Productor agrícola, finca mixta caña/limón (Tafí Viejo / Lules)

---

## Segmentos Secundarios

### Bomberos Voluntarios y Brigadistas Forestales

Deben intervenir en incendios rurales muchas veces sin información precisa sobre la ubicación del foco ígneo. Esto aumenta considerablemente el riesgo operativo y dificulta el acceso rápido al lugar debido a caminos rurales en mal estado, tranqueras cerradas o grandes distancias.

> *"Llegamos siempre a ciegas. La gente llama desesperada cuando el fuego ya tiene cinco metros de alto. El mayor problema es entrar al campo: nos metemos por caminos de tierra y terminamos topándonos con tranqueras cerradas con candado. Perdemos tiempo valioso buscando por dónde pasar el autobomba."*
> — Bombero Voluntario, cuartel zona de interfase (Yerba Buena / San Javier)

### Compañías de Seguros Agrícolas

Afrontan altos costos económicos debido a la creciente cantidad de siniestros rurales ocasionados por incendios. Buscan constantemente mecanismos preventivos que reduzcan riesgos y permitan validar que los productores implementen medidas de monitoreo y prevención.

> *"En el NOA, y sobre todo en Tucumán durante la primavera, la siniestralidad se nos va por las nubes. Las sequías extremas nos hicieron pagar pólizas millonarias por lotes enteros quemados. Si un cliente me demuestra que con tu sensor bajó su tiempo de respuesta de una hora a diez minutos, su riesgo de pérdida total se desploma."*
> — Ejecutivo de compañía de seguros agrícolas, San Miguel de Tucumán

### Responsables de Higiene y Seguridad Industrial

Ingenios azucareros y grandes agroindustrias donde los incendios representan un riesgo directo para la vida de operarios, maquinistas y personal de campo. Necesitan activar protocolos de evacuación de manera rápida para cumplir normativas de seguridad laboral (SRT).

> *"Un fuego descontrolado no es solo un problema de Medio Ambiente, es un riesgo crítico para la vida de la gente. La zafra no frena, tenemos máquinas cosechadoras y tractores trabajando a mil por hora. Nuestro mayor miedo es que el fuego, con los vientos de agosto, arrincone a un maquinista."*
> — Responsable de Higiene y Seguridad, ingenio azucarero

### Comunidades Rurales y Trabajadores Agrícolas

Sufren consecuencias directas del humo, la contaminación ambiental, los riesgos sanitarios y la posible pérdida de fuentes de trabajo cuando las producciones se ven afectadas por incendios.

---

*Documento perteneciente al proyecto Sistema de Alerta de Incendios Rurales*
*Fuentes: Entrevistas realizadas a productores, bomberos, aseguradores y responsables de seguridad (Tucumán, 2026)*
