pinto0528/alpa/Documentacion/Validacion/soluciones_actuales.md

# Soluciones Actuales

## Acciones que Toma Hoy

Los productores agropecuarios implementan distintos métodos manuales para intentar prevenir o detectar incendios rurales:

| Acción | Descripción | Limitación |
|---|---|---|
| **Recorridos de vigilancia** | Patrullajes en motos, camionetas o tractores por el campo, especialmente durante épocas críticas de sequía y zafra | Imposible cubrir grandes extensiones 24/7. De noche o en zonas alejadas, la vigilancia es nula |
| **Personal de guardia** | Asignar empleados encargados de monitorear visualmente distintas zonas de la finca | Requiere mano de obra dedicada. No escala. El error humano es frecuente |
| **Cortafuegos manuales** | Cuando se detecta un foco, enganchan rastras al tractor para crear cortafuegos y evitar la propagación | Para cuando lo hacen, el fuego ya avanzó. 30-40 minutos de demora |
| **Comunicación por radios** | Coordinación mediante radios rurales o llamadas telefónicas cuando hay señal | Depende de que haya cobertura. En zonas profundas del campo, no hay señal |
| **Red de vecinos** | Depender de que un vecino o transeúnte vea humo y avise | Tardío e impredecible. El vecino puede estar a kilómetros |

---

## Herramientas que Usa

| Herramienta | Uso | Efectividad |
|---|-----|---|
| Radios de comunicación rural | Coordinación interna y aviso a cuarteles | Limitada por alcance y cobertura |
| Tractores y rastras | Crear cortafuegos manuales | Reactivo, no preventivo |
| Vigilancia humana | Detección visual de humo o fuego | Solo de día, solo donde hay ojos |
| Protocolos manuales de evacuación | Sacar personal del campo ante incendio | Lentos, dependen de comunicación previa |
| Grupos de WhatsApp/vecinos | Aviso entre productores y trabajadores | Depende de conectividad celular |
| Vehículos de recorrida | Monitoreo visual por el campo | Cobertura limitada, costoso en combustible |

---

## Limitaciones de las Soluciones Actuales

### Dependencia total de la observación humana

El incendio solo es detectado cuando alguien logra ver humo o fuego, lo cual **generalmente ocurre demasiado tarde**. No hay detección automática ni en etapa incipiente.

### Imposibilidad de cobertura total

Las grandes extensiones rurales hacen **imposible controlar permanentemente todos los sectores** del campo. Durante la noche o en zonas alejadas la vigilancia se vuelve aún más difícil.

> *"De noche o en los fondos de la finca es imposible tener ojos en todos lados."*
> — Productor agrícola, Tafí Viejo

### Falta de conectividad

La ausencia de señal celular en áreas rurales representa un **obstáculo importante** para comunicar rápidamente la emergencia y coordinar acciones.

### Cadena de aviso lenta e ineficiente

El proceso actual de detección y aviso sigue esta cadena:

```
Foco ígneo se inicia
    │
    ▼ (sin detección automática)
Alguien ve humo (30+ minutos después)
    │
    ▼ (depende de que haya alguien mirando)
Avisa por radio/teléfono (si hay señal)
    │
    ▼
Base avisa al responsable
    │
    ▼
Responsable coordina respuesta
    │
    ▼
Fuego ya es incontrolable
```

**Resultado:** demoras críticas en los primeros minutos del incendio, que son los más importantes para la contención.

---

## Gaps No Cubiertos

Actualmente **no existe** una solución eficiente que permita realizar detección automática y temprana de incendios rurales en zonas agrícolas con infraestructura limitada.

### Lo que los usuarios necesitan y no encuentran

| Necesidad | Gap actual |
|---|---|
| **Detección automática de humo/fuego** | No hay ningún sistema que detecte el foco apenas se inicia sin depender de un observador humano |
| **Alertas inmediatas con ubicación GPS** | Los avisos actuales son manuales, tardíos y sin geolocalización precisa |
| **Funcionamiento sin señal celular** | Las soluciones existentes requieren conectividad que no existe en zonas rurales profundas |
| **Reportes digitales automáticos** | No hay forma de generar evidencia digital para seguros, auditorías y cumplimiento normativo |
| **Reducción del tiempo de respuesta** | El tiempo actual (30-40 minutos) es inaceptable. Se necesita detección en los primeros 5-15 minutos |
| **Mejora de seguridad del personal** | No hay sistema que permita activar protocolos de evacuación de forma inmediata y automatizada |

### Lo que dicen los stakeholders

> *"Si tu sistema nos manda las coordenadas GPS exactas al celular cuando recién es una chispa, nosotros mandamos rápido una camioneta liviana con cuatro chicos y mochilas de agua, y lo apagamos en diez minutos."*
> — Bombero Voluntario

> *"Si un cliente me demuestra que con tu sensor bajó su tiempo de respuesta de una hora a diez minutos, su riesgo de pérdida total se desploma. Yo le puedo justificar a la casa central una baja en el costo de su póliza sin problema."*
> — Ejecutivo de seguros agrícolas

> *"Eso sí: el dispositivo me tiene que generar un reporte en la nube, algo inalterable, que a mí me certifique que el equipo estaba encendido y monitoreando cuando arrancó el siniestro."*
> — Ejecutivo de seguros agrícolas

---

## Oportunidad

Estos vacíos representan la principal oportunidad para el desarrollo de un **sistema inteligente de alerta temprana de incendios rurales** que:

1. Detecte automáticamente focos ígneos en etapa incipiente
2. Envíe alertas con geolocalización precisa
3. Funcione de forma autónoma en zonas sin infraestructura
4. Genere reportes digitales para seguros y auditorías
5. Permita activar protocolos de evacuación de forma inmediata
6. Reduzca el tiempo de respuesta de 30-40 minutos a menos de 5 minutos

---

*Documento perteneciente al proyecto Sistema de Alerta de Incendios Rurales*
*Fuentes: Entrevistas realizadas a productores, bomberos, aseguradores y responsables de seguridad (Tucumán, 2026)*
