pinto0528/alpa/Documentacion/Entregables_concurso/Entregable_4/one_pager_guia.md

# ¿Qué es un One Pager y cuál es su propósito?

El **One Pager** es un documento de una sola página que contiene un resumen ejecutivo de una startup. Es un material imprescindible para dar a conocer tu proyecto empresarial a los inversores. Contiene toda la información básica de la empresa, como el tamaño del mercado o el equipo. Toda la información debe caber en **una sola cara de una hoja A4**, ni más ni menos.

Es la carta de presentación para los inversores. Por ello, es importante trabajar el documento, ya que será la primera impresión que tendrán sobre la empresa. A los inversores les bastan **10 segundos** para decidir si continúan leyendo tu One Pager. Tiene que ser claro, conciso y con un diseño de fácil lectura.

## Requisitos fundamentales

- **Formato A4 o equivalente:** Los documentos de tamaño A4 son el estándar para la comunicación formal de una página.
- **Imprimibles:** Suelen distribuirse de forma digital, pero es probable que se impriman para leer con concentración. Es importante utilizar un formato adecuado para la impresión (márgenes adecuados).
- **Una sola cara:** Como su nombre indica, toda la información tiene que estar comprimida en una página.
- **Buena distribución del contenido:** Dependiendo del One Pager, puedes distribuir el contenido utilizando columnas, espacios razonables entre párrafos, partes del texto en negrita, subtítulos o destacados, etc.

Además, un One Pager no solo crea una primera impresión positiva y profesional, sino que también facilita el inicio de conversaciones más profundas con inversores o clientes potenciales. Su diseño atractivo y conciso lo convierte en una opción ideal para eventos de networking, presentaciones y material de marketing digital.

---

## Elementos clave que debe incluir un One Pager

### 1. Logotipo y tagline (slogan)

El logotipo de tu empresa es la representación visual de tu marca y debe ser prominente en el One Pager. Asegúrate de incluir una versión de alta calidad de tu logotipo que refleje la identidad y los valores de tu negocio.

Justo debajo o al lado del logotipo, incluye tu tagline, una frase breve que capture la esencia de lo que ofreces. El tagline debe ser impactante y memorable, ya que actúa como un ancla que ayuda a los lectores a recordar tu propuesta de valor.

### 2. Perfil del proyecto o empresa

Ofrece una visión general que ayude a los lectores a comprender rápidamente tu misión y visión. Comienza con una breve descripción que resuma quién eres, qué haces y por qué es importante, a qué sector pertenece, en qué fase se encuentra.

Este resumen debe incluir detalles fundamentales como el segmento de mercado al que te diriges y los problemas que estás resolviendo. Destaca los valores fundamentales que guían tu negocio.

### 3. Problema y solución

Identificar claramente el problema que tu negocio busca resolver. Comienza describiendo la situación actual o el desafío específico que enfrentan tus clientes potenciales.

A continuación, presenta tu solución de manera clara y concisa. Explica cómo tus productos o servicios abordan y resuelven el problema identificado. Destaca los beneficios tangibles que los clientes experimentarán al elegir tu oferta.

### 4. Modelo de negocio y plan estratégico

Describe cómo planeas generar ingresos y operar de manera sostenible. Explica los diferentes flujos de ingresos, como ventas de productos, suscripciones, o servicios. Define tu propuesta de valor única y cómo se diferencia de la competencia.

Incluye un breve resumen de tu plan estratégico que aborde tus objetivos a corto y largo plazo. Esto puede incluir hitos importantes, estrategias de marketing, y cómo planeas escalar tu negocio.

### 5. Equipo y tracción

Presenta a los miembros clave del equipo, incluyendo sus roles, experiencia y habilidades relevantes. Resalta sus logros previos y cómo su experiencia contribuye al éxito de tu proyecto.

Incluye información sobre la tracción que ha ganado tu negocio: métricas clave como crecimiento de usuarios, cifra de ventas, alianzas estratégicas, o cualquier reconocimiento recibido.

### 6. Llamada a la Acción

Termina con una clara llamada a la acción que invite a los lectores a dar el siguiente paso, ya sea programar una reunión, visitar tu sitio web o inscribirse en un boletín.

---

## Cómo diseñar un One Pager

1. **Selecciona un formato limpio y organizado:** Utiliza un diseño que facilite la lectura. Información estructurada en secciones claramente definidas, usando encabezados y subtítulos.

2. **Utiliza colores y fuentes coherentes:** Elige una paleta de colores que refleje la identidad de tu marca. Tipografía consistente, legible y apropiada para tu audiencia.

3. **Incorpora elementos visuales:** Gráficos, iconos o imágenes pueden ayudar a ilustrar tus puntos y hacer que el contenido sea más atractivo.

4. **Mantén un equilibrio entre texto e imágenes:** El texto debe ser conciso y directo. Evita párrafos largos y utiliza bullets o listas para resumir información clave.

5. **Revisa y ajusta el contenido final:** Revisa cuidadosamente el texto en busca de errores gramaticales y ortográficos. Solicita la opinión de otras personas para obtener retroalimentación.
