pinto0528/alpa/Documentacion/Entregables_concurso/Entregable_4/pautas.md

# Pautas para armar Pitch

## Problema
Describir las principales causas y consecuencias del problema, aportando cifras importantes que permitan cuantificarlo. Demostrar entendimiento profundo del problema desde la necesidad del cliente/usuario.

## Principales clientes o usuarios
Identificar claramente un segmento de usuarios y/o clientes. Profundizar en quiénes serán sus primeros clientes/usuarios.

## Competencia
Explicar cómo se intenta solucionar actualmente el problema y quiénes son los principales competidores y/o sustitutos.

## Propuesta de valor
Describir la solución innovadora, demostrando el valor que entrega a los usuarios y/o clientes y cómo soluciona su problema. Mostrar el prototipo, las ventajas únicas del proyecto y cómo se diferencia de la competencia.

## Equipo
Describir las habilidades y conocimientos de cada integrante del equipo, sus pasiones, compromiso y motivaciones por llevar a cabo el emprendimiento.

## Presentación
El PDF, PPT, y/o video de apoyo es efectivo, atractivo, informativo y complementa el pitch. Presentación oral clara y completa.
