pinto0528/alpa/Documentacion/Presentacion_general/one_pager.pdf

# Alerta Temprana contra Incendios Rurales

CUIDAMOS TU CAMPO

## Emprende U · 2026

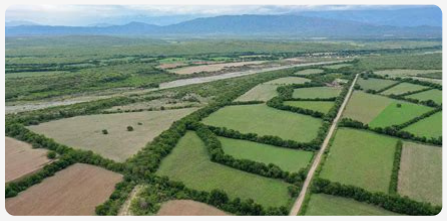
[picture p4: figure]

ALPA es un sistema autónomo de
detección temprana de incendios rurales, diseñado para productores que operan en zonas con escasa o nula conectividad.

Sector: agrotech / IoT.
Fase actual: prototipo funcional validado.

# Problema

10.000+ incendios rurales por año en Argentina. Tucumán 2025, 55.870 hectáreas afectadas.
El 95% pudo evitarse con detección temprana.
El productor descubre el fuego 30–40 minutos después

No existe una solución accesible diseñada para zonas sin conectividad.

ALPA monitorea el campo 24/7 de forma automatizada, sin tener que esperar a que alguien vea el humo.

Sensores de temperatura, llama y humo
Comunicación de 5 a 10 km de distancia por nodo. Sin celular, sin internet, sin operador.
Autonomia extendida hasta 2-3 meses.
Alerta en dashboard web y notificación al productor.

Modelo de negocio : Kit hardware + suscripción anual.

Canales: directo (productor), B2B (aseguradoras), B2G (gobierno). Mercado direccionable: +12.000 productores en el NOA.

Equipo N.T.

Mario Roberto Quiroga | — Full-Stack
Jeremias Mastafa Nazar | — Firmware
Gonzalo Fabricio Lescano — Negocio
Nicolas Pinto | — Hardware
Contacto: nicolaspinto2805@gmail.com

CUIDAMOS TU CAMPO
