pinto0528/alpa/Comunicacion/Assets/cuadro.png

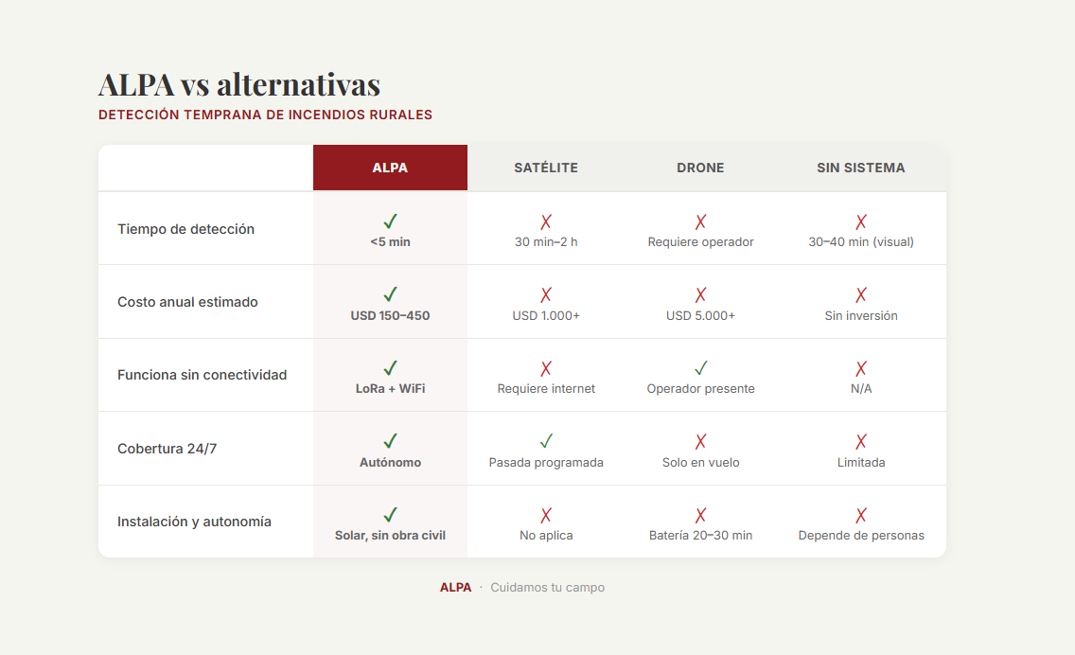
Comunicacion/Assets/cuadro.png
