pinto0528/alpa/Comunicacion/Assets/mood2.jpg

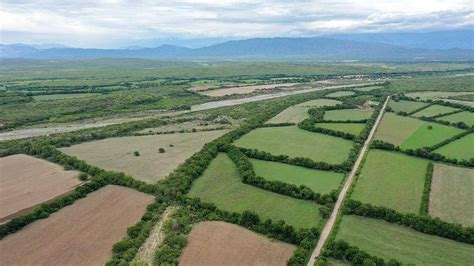
Comunicacion/Assets/mood2.jpg
