pinto0528/alpa/Comunicacion/Assets/mood3.jpg

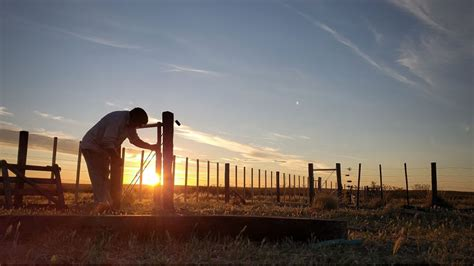
Comunicacion/Assets/mood3.jpg
