pinto0528/alpa/Comunicacion/Assets/mood4.jpg

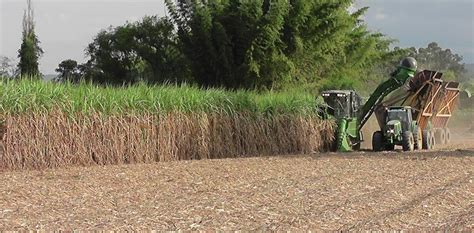
Comunicacion/Assets/mood4.jpg
