pinto0528/alpa/Comunicacion/Assets/mood6.jpg

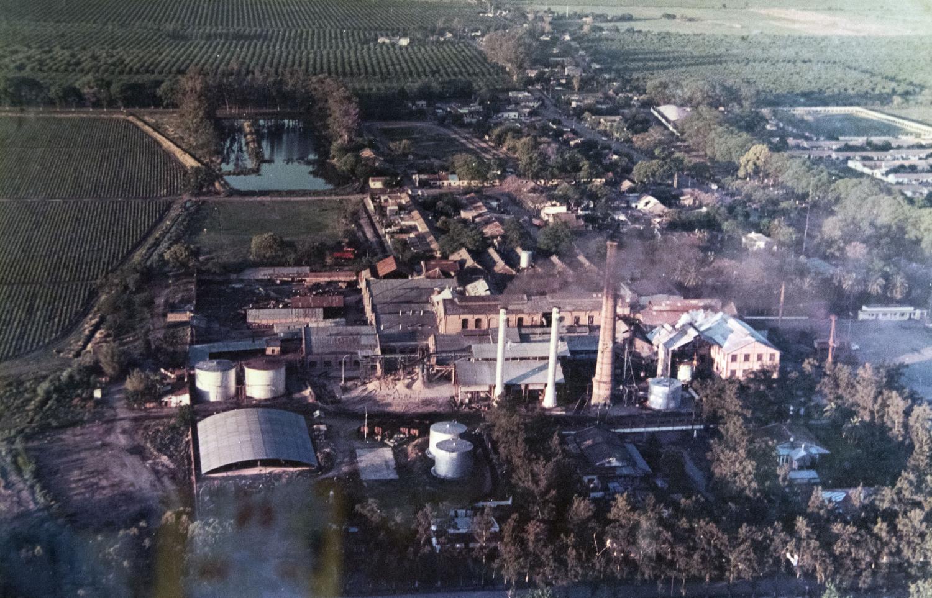
Comunicacion/Assets/mood6.jpg
