pinto0528/alpa/Comunicacion/Assets/poncho.png

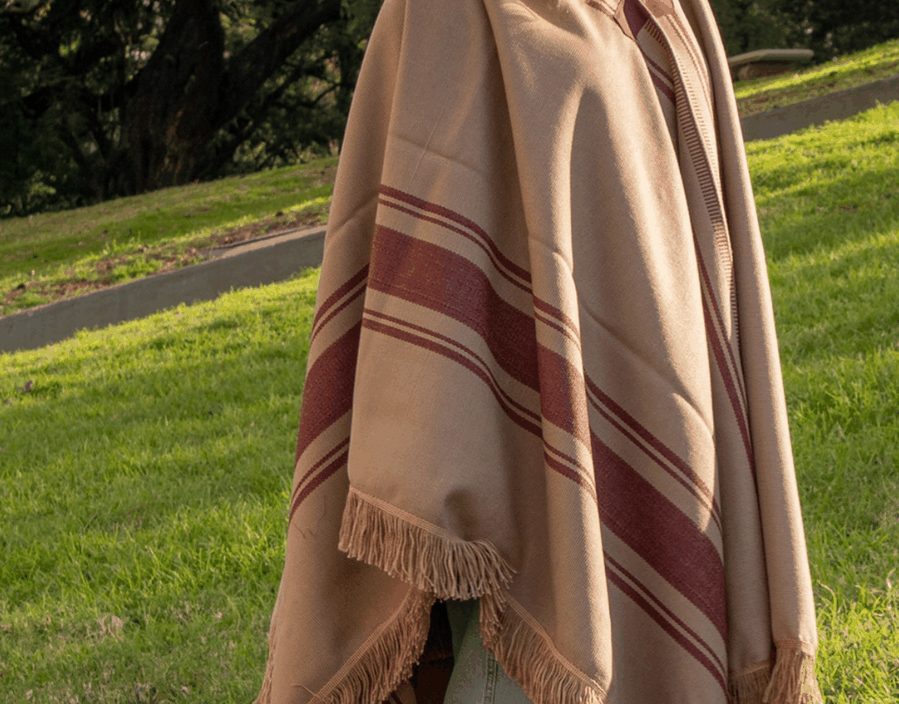
Comunicacion/Assets/poncho.png
