pinto0528/alpa/Documentacion/Entregables_concurso/Entregable_4/entregable_4_cover.jpg

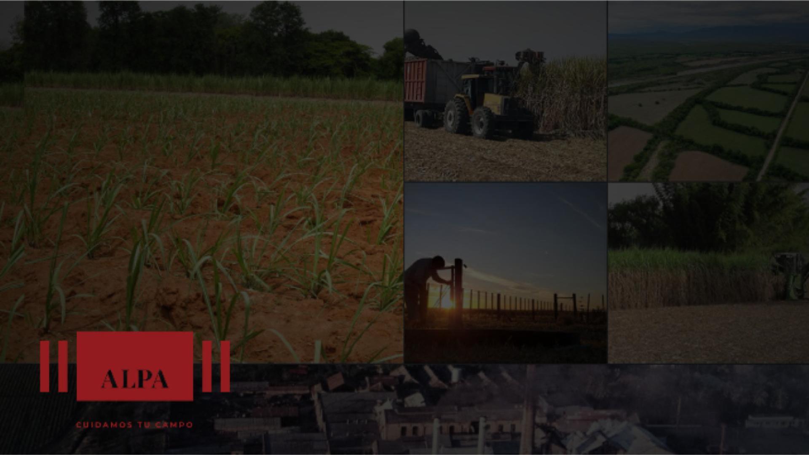
Documentacion/Entregables_concurso/Entregable_4/entregable_4_cover.jpg
